LinuxDinoGitHub/Squawk-2.0/Assets/Radio_ortho.png

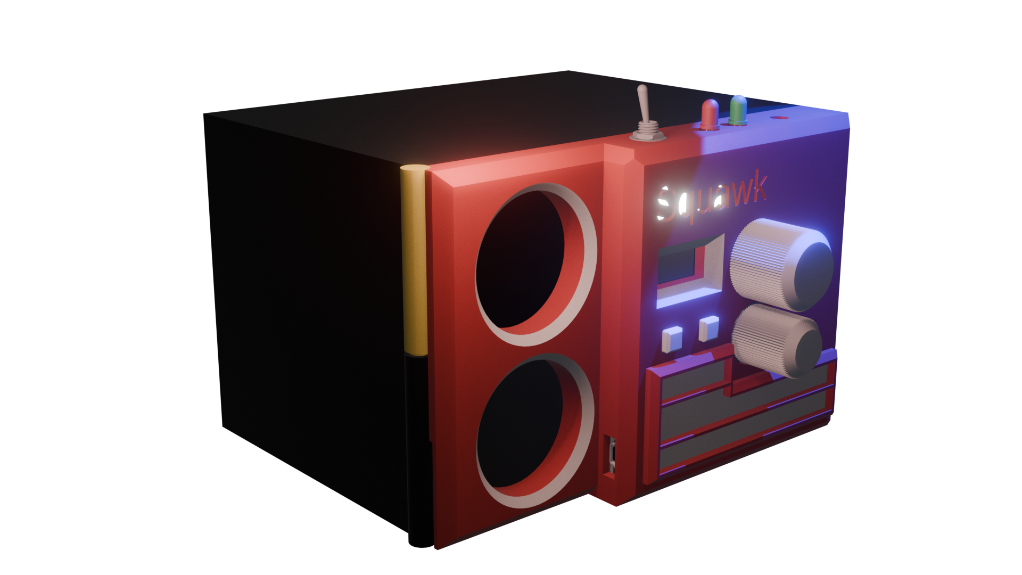
Assets/Radio_ortho.png
