LinuxDinoGitHub/Squawk-2.0/Assets/Screenshot 2026-04-25 143108.png

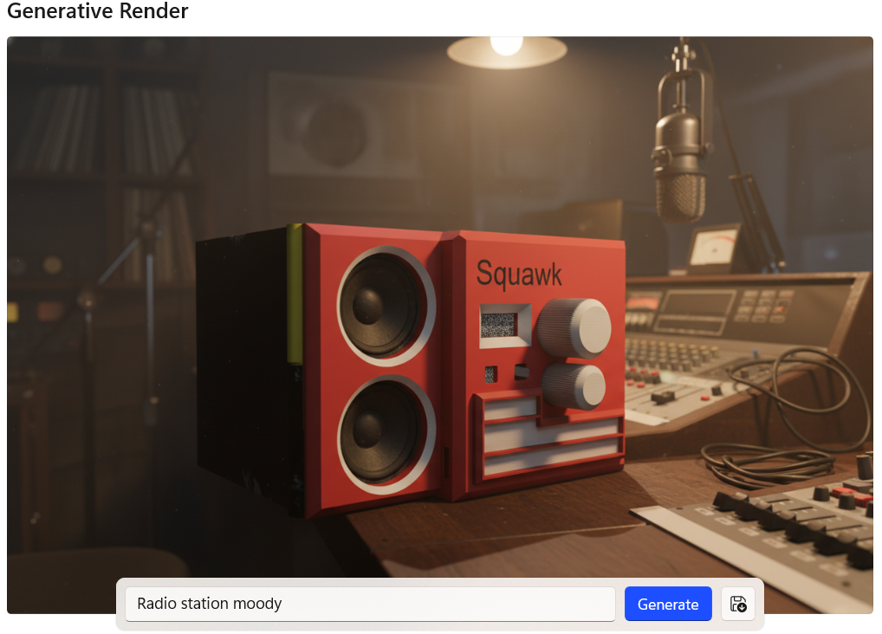
Assets/Screenshot 2026-04-25 143108.png
