LinuxDinoGitHub/Squawk-2.0/Assets/Screenshot 2026-04-27 235243.png

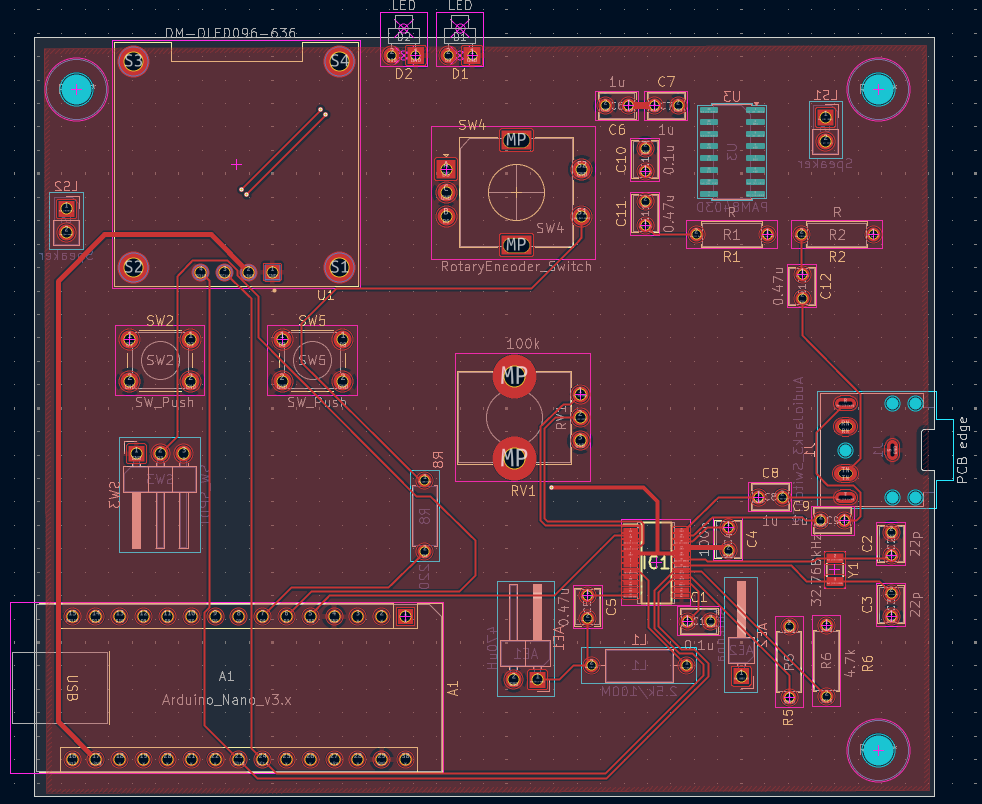
Assets/Screenshot 2026-04-27 235243.png
