LinuxDinoGitHub/Squawk-2.0/Assets/Print Schematic.png

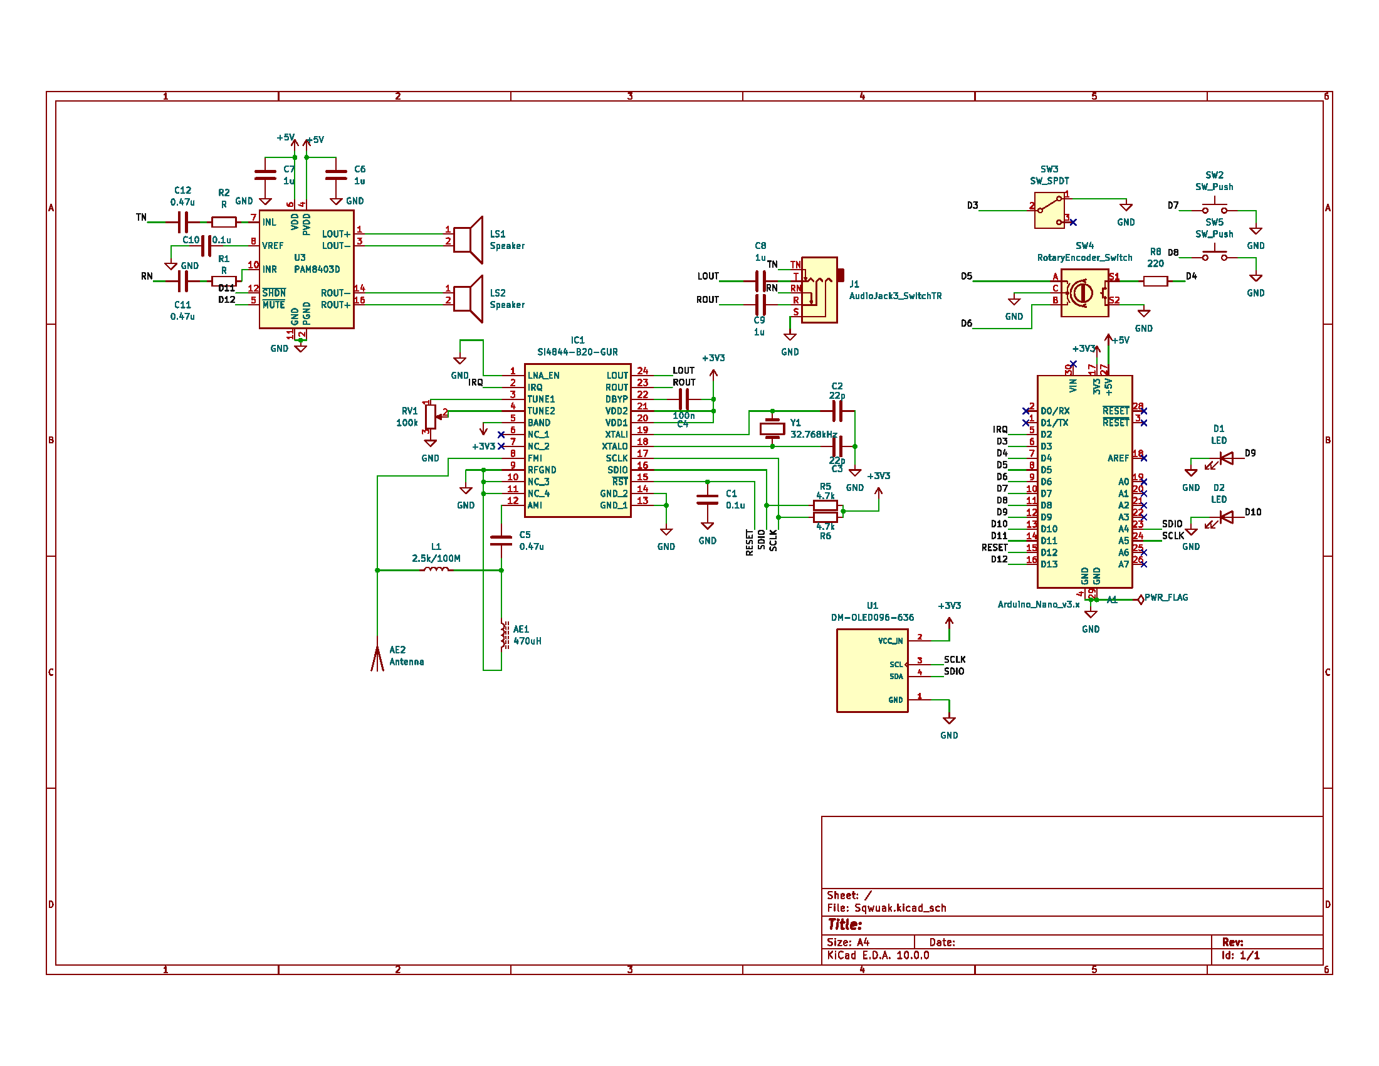
Assets/Print Schematic.png
